hardesk/zxx-pcb/tools/isr.c

// This file is Copyright (c) 2020 Florent Kermarrec <florent@enjoy-digital.fr>
// License: BSD

#include <csr.h>
#include <soc.h>
#include <irq_vex.h>
#include <uart.h>
#include <defs.h>

//#ifdef CONFIG_CPU_HAS_INTERRUPT

uint16_t isr_flag;

// Handy macro
#define ISR_SECTION  __attribute__((section(".text.isr"))) __attribute__((used))

ISR_SECTION void isr(void)
{
//	__attribute__((unused)) unsigned int irqs;
//
//	irqs = irq_pending() & irq_getmask();
//
	irq_setmask(0);
    reg_timer0_irq_en = 0; // disable interrupt

//    reg_debug_irq_en = 0;
//    reg_reset = 1;
//    asm volatile ("slli x0, x0, 0x1f");
//    asm volatile ("ebreak");
//    asm volatile ("srai x0, x0, 7");

//   reg_la1_data = 0xa;
//   reg_la0_data = 0x20000;
   reg_timer0_update = 1;
   if (reg_timer0_value == 0)
       isr_flag = 1;
   else
       reg_timer0_irq_en = 1;

//	if(irqs & (1 << TIMER0_INTERRUPT)) {
////		uart_isr();
//        reg_la1_data = 0xa;	// Signal end of test 1st stage
//        reg_la0_data = 0x20000;
//        flag = 1;
//    }
    return;

//#ifndef UART_POLLING
//	if(irqs & (1 << UART_INTERRUPT))
//		uart_isr();
//#endif
}

//#else
//
//void isr(void){};
//
//#endif
